minato8080/IndoorMultiSensor/kiCad/IndoorMultiSensor.kicad_sch

## KiCad design kiCad/IndoorMultiSensor.kicad_sch (2024-10-05, an earlier design)

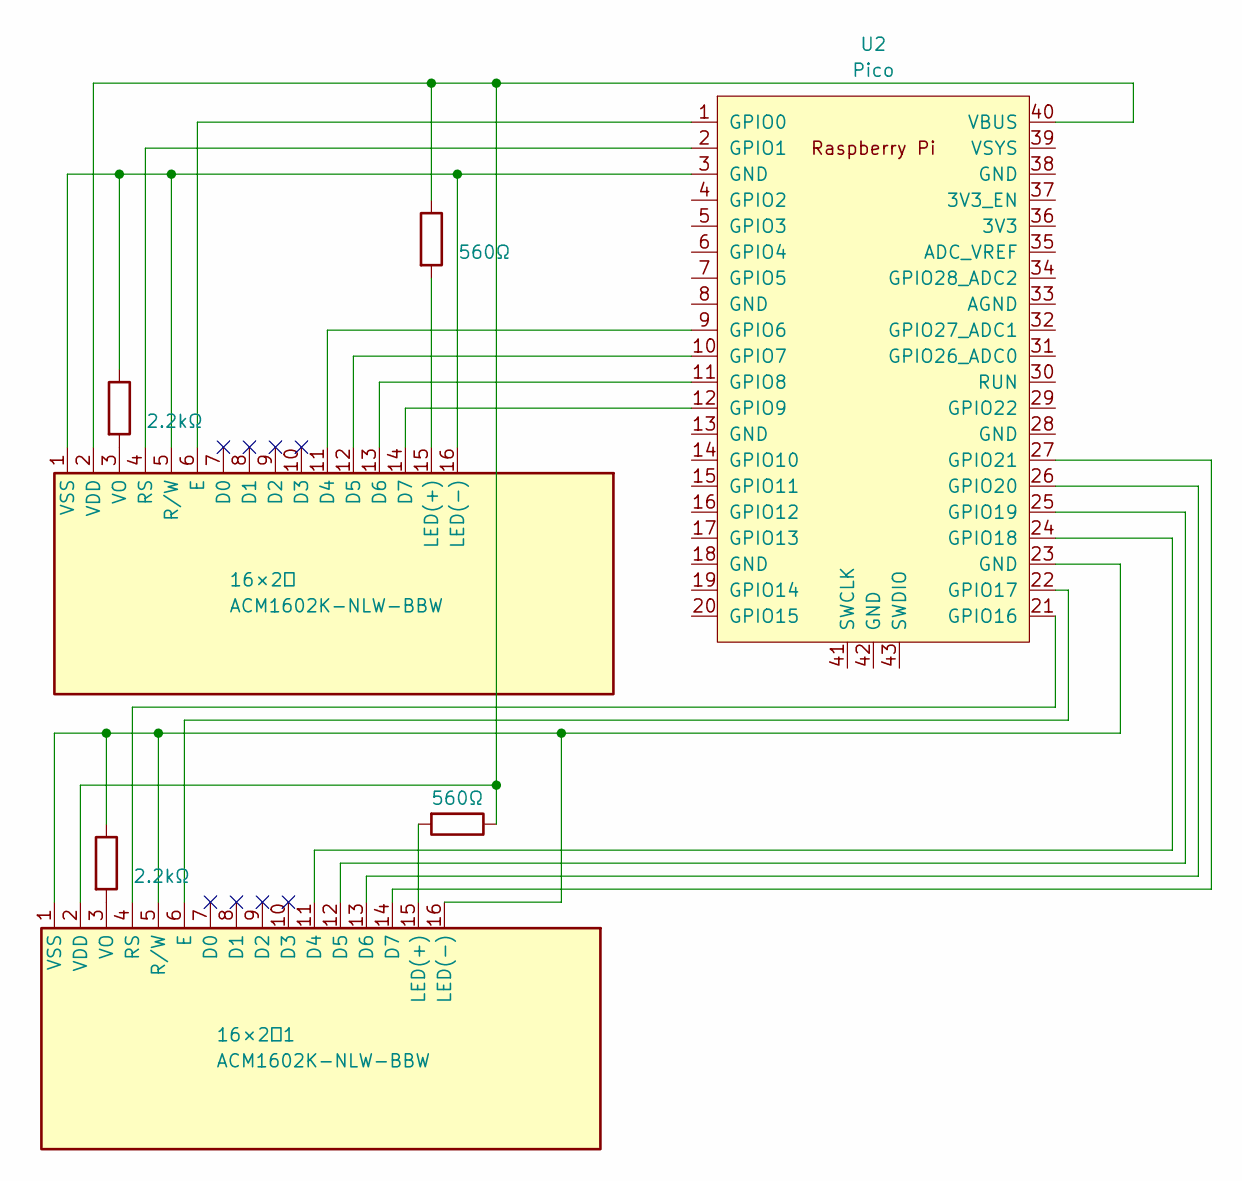
[picture p2: schematic IndoorMultiSensor.kicad_sch]

Parts:
16×2行, 16×2行1: ACM1602K-NLW-BBW; WC1602A
R1, R4: 560Ω
R2, R3: 2.2kΩ
U2: Pico; RPi_Pico_SMD_TH

Connections:
unnamed: 16×2行1.1 (VSS), 16×2行1.5 (R/W), 16×2行1.16 (LED(-)), R3.1, U2.23 (GND)
unnamed: 16×2行1.3 (VO), R3.2
unnamed: 16×2行1.4 (RS), U2.21 (GPIO16)
unnamed: 16×2行1.6 (E), U2.22 (GPIO17)
unnamed: 16×2行1.11 (D4), U2.24 (GPIO18)
unnamed: 16×2行1.12 (D5), U2.25 (GPIO19)
unnamed: 16×2行1.13 (D6), U2.26 (GPIO20)
unnamed: 16×2行1.14 (D7), U2.27 (GPIO21)
unnamed: 16×2行1.15 (LED(+)), R4.2
unnamed: 16×2行.1 (VSS), 16×2行.5 (R/W), 16×2行.16 (LED(-)), R2.1, U2.3 (GND)
unnamed: 16×2行.2 (VDD), 16×2行1.2 (VDD), R1.1, R4.1, U2.40 (VBUS)
unnamed: 16×2行.3 (VO), R2.2
unnamed: 16×2行.4 (RS), U2.2 (GPIO1)
unnamed: 16×2行.6 (E), U2.1 (GPIO0)
unnamed: 16×2行.11 (D4), U2.9 (GPIO6)
unnamed: 16×2行.12 (D5), U2.10 (GPIO7)
unnamed: 16×2行.13 (D6), U2.11 (GPIO8)
unnamed: 16×2行.14 (D7), U2.12 (GPIO9)
unnamed: 16×2行.15 (LED(+)), R1.2
